DanJMaher/Power-Distribution-Board/main/data.cpp

/**
 * data.cpp
 * *************************
 * For Kent State's ATR Lab  
 * 03/19/2021
 * Dan Maher
 * 
 * Code for operation of revision 1 of the custom 
 * power distribution board (PDB) PCB 
 * 
 * *******************************************************
 * The Data class provides a central storage location for
 * voltage, relay status, and time. The Comm class
 * generates a JSON document using data stored in a
 * Data object.
 * *******************************************************
**/

/******************************/
/**********HEADERS*************/
/******************************/
#include "data.h"

/********************************/
/***********DEFINITIONS**********/
/********************************/
void Data::storeTime(unsigned long t){
  storedTime = t;
  storedMillis = millis();
}

unsigned long Data::retrieveTime(){
  unsigned long currentTime = storedTime + (millis() - storedMillis)/1000;
  return currentTime;
}

void Data::setVoltage_11(float v){voltage_11 = v;}
void Data::setVoltage_22(float v){voltage_22 = v;}
void Data::setRelayStatus_11(bool r){relay_11 = r;}
void Data::setRelayStatus_22(bool r){relay_22 = r;}

float Data::getVoltage_11(){return voltage_11;}
float Data::getVoltage_22(){return voltage_22;}
bool Data::getRelay_11(){return relay_11;}
bool Data::getRelay_22(){return relay_22;}
